Kampi/BeeLight/docs/images/Photo_1.png

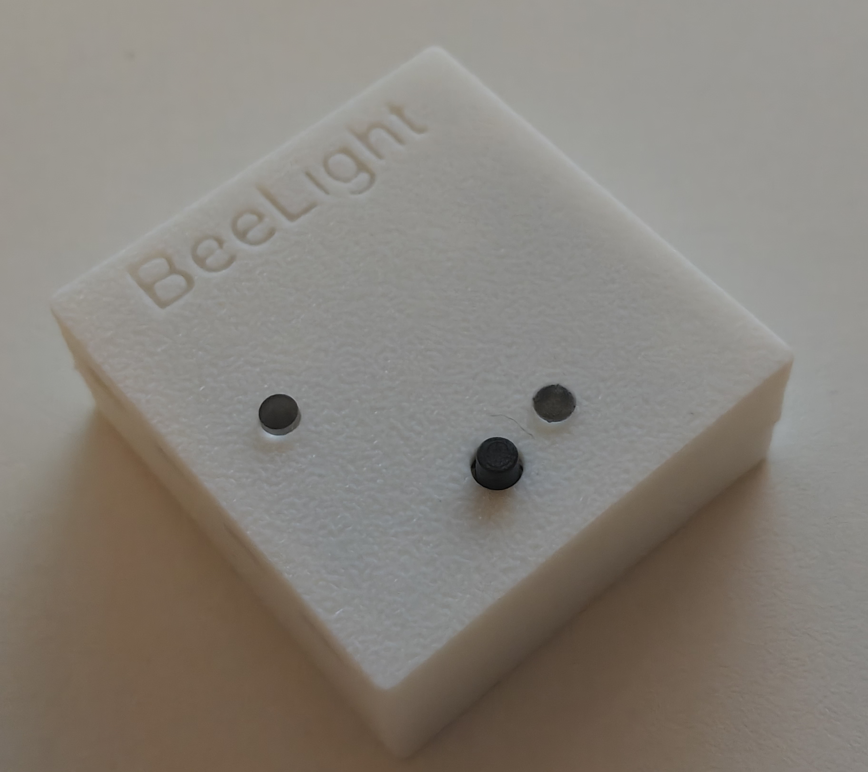
docs/images/Photo_1.png
