Kampi/BeeLight/firmware/app/src/beelight/beelight_bsec2.h

/*
 * This file is part of the BeeLight project <https://github.com/Kampi/BeeLight>.
 * Copyright (c) 2026 Daniel Kampert.
 *
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
 * You should have received a copy of the GNU General Public License
 * along with this program. If not, see <http://www.gnu.org/licenses/>.
 */

#pragma once

#include <zb_ha_device_config.h>

/** @brief See https://zigbeealliance.org/wp-content/uploads/2021/10/07-5123-08-Zigbee-Cluster-Library.pdf for additional informations
 *  @details
 *          Server
 *              - @ref ZB_ZCL_BASIC \n
 *              - @ref ZB_ZCL_IDENTIFY \n
 *              - @ref ZB_ZCL_CLUSTER_ID_POWER_CONFIG \n
 *              - @ref ZB_ZCL_CLUSTER_ID_ILLUMINANCE_MEASUREMENT \n
 *              - @ref ZB_ZCL_CLUSTER_ID_TEMP_MEASUREMENT \n
 *              - @ref ZB_ZCL_CLUSTER_ID_PRESSURE_MEASUREMENT \n
 *              - @ref ZB_ZCL_CLUSTER_ID_REL_HUMIDITY_MEASUREMENT \n
 *              - @ref ZB_ZCL_CLUSTER_ID_CO2_MEASUREMENT \n
 *              - @ref ZB_ZCL_CLUSTER_ID_IAQ_MEASUREMENT \n
 *              - @ref ZB_ZCL_CLUSTER_ID_VOC_MEASUREMENT \n
 *
 *          Client
 *              -
 */

/** @brief Number of IN (server) clusters.
*/
#define BEELIGHT_IN_CLUSTER_NUM             10

/** @brief Number of OUT (client) clusters.
*/
#define BEELIGHT_OUT_CLUSTER_NUM            1

/** @brief Number of attributes.
*/
#define BEELIGHT_REPORT_ATTR_COUNT          10

/** @brief                              Declare the cluster list for the Environment Sensor device.
 *  @param cluster_list_name            Cluster list variable name
 *  @param basic_attr_list              Attribute list for Basic cluster
 *  @param identify_client_attr_list    Attribute list for Identify cluster (Client)
 *  @param identify_server_attr_list    Attribute list for Identify cluster (Server)
 *  @param power_attr_list              Attribute list for Power cluster
 *  @param illu_attr_list               Attribute list for Illuminance Measurement cluster
 *  @param temp_attr_list               Attribute list for Temperature Measurement cluster
 *  @param pres_attr_list               Attribute list for Pressure Measurement cluster
 *  @param hum_attr_list                Attribute list for Humidity Measurement cluster
 *  @param co2_attr_list                Attribute list for CO2 cluster
 *  @param iaq_attr_list                Attribute list for IAQ Measurement cluster
 *  @param voc_attr_list                Attribute list for VOC Measurement cluster
 */
#define BEELIGHT_DECLARE_CLUSTER_LIST(                                      \
    cluster_list_name,                                                      \
    basic_attr_list,                                                        \
    identify_server_attr_list,                                              \
    identify_client_attr_list,                                              \
    power_attr_list,                                                        \
    illu_attr_list,                                                         \
    temp_attr_list,                                                         \
    pres_attr_list,                                                         \
    hum_attr_list,                                                          \
    co2_attr_list,                                                          \
    iaq_attr_list,                                                          \
    voc_attr_list)                                                          \
    static zb_zcl_cluster_desc_t cluster_list_name[] =                      \
    {                                                                       \
        BEELIGHT_CLUSTER_BASIC_DESC(basic_attr_list)                        \
        BEELIGHT_CLUSTER_IDENTIFY_SERVER_DESC(identify_server_attr_list)    \
        BEELIGHT_CLUSTER_POWER_DESC(power_attr_list)                        \
        BEELIGHT_CLUSTER_ILLUMINANCE_DESC(illu_attr_list)                   \
        BEELIGHT_CLUSTER_TEMP_DESC(temp_attr_list)                          \
        BEELIGHT_CLUSTER_PRESSURE_DESC(pres_attr_list)                      \
        BEELIGHT_CLUSTER_HUMIDITY_DESC(hum_attr_list)                       \
        BEELIGHT_CLUSTER_CO2_DESC(co2_attr_list)                            \
        BEELIGHT_CLUSTER_IAQ_DESC(iaq_attr_list)                            \
        BEELIGHT_CLUSTER_VOC_DESC(voc_attr_list)                            \
        BEELIGHT_CLUSTER_IDENTIFY_CLIENT_DESC(identify_client_attr_list)    \
    }

/** @brief                  Declare simple descriptor for the Environment Sensor device.
 *  @param ep_name          Endpoint variable name
 *  @param ep_id            Endpoint ID
 *  @param in_clust_num     Number of supported input clusters
 *  @param out_clust_num    Number of supported output clusters
 */
#define BEELIGHT_DECLARE_SIMPLE_DESC(ep_name, ep_id, in_clust_num, out_clust_num) \
    ZB_DECLARE_SIMPLE_DESC(in_clust_num, out_clust_num); \
    ZB_AF_SIMPLE_DESC_TYPE(in_clust_num, out_clust_num) simple_desc_##ep_name = \
    { \
        ep_id, \
        ZB_PROFILE_ID, \
        ZB_DEVICE_ID, \
        ZB_DEVICE_VER, \
        0, \
        in_clust_num, \
        out_clust_num, \
        { \
            BEELIGHT_CLUSTER_IDS_EXTENDED \
            ZB_ZCL_CLUSTER_ID_IDENTIFY, \
        } \
    }
